AlbinoBoii/Student-Life-Track-2026/washer_monitor/washer_logic.h

#pragma once
#include <Arduino.h>

enum WasherState {
  IDLE_STATE,
  RUNNING_STATE
};

void initWasherLogic();
void updateWasherState(float motionScore);
WasherState getWasherState();
const char* washerStateName();
